axecosinussoft/CleanHeat/1. 3D Models/1.1 MVP-2 (Slider)/1.1.1 3D-Models — SolidWorks 2019/1. Детали/Модуль Micro зарядки Type С.SLDPRT

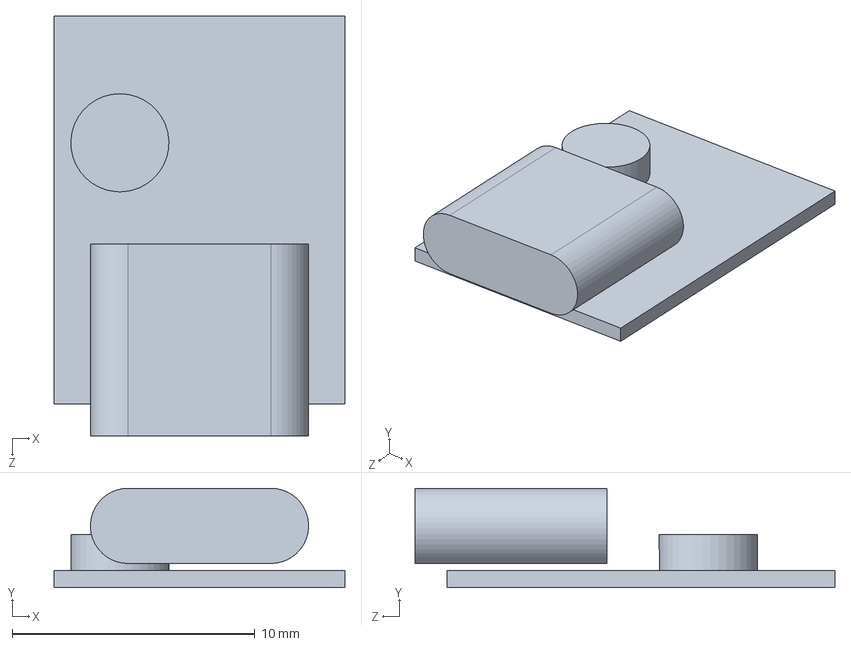
[picture p17: CAD file, 2026-01-13]
1. 3D Models/1.1 MVP-2 (Slider)/1.1.1 3D-Models — SolidWorks 2019/1. Детали/Модуль Micro зарядки Type С.SLDPRT
12.0 x 4.10 x 17.3 mm
