axecosinussoft/CleanHeat/1. 3D Models/1.1 MVP-2 (Slider)/1.1.2 3D-Print — STL/2. Каретка патрона form — Black.STL

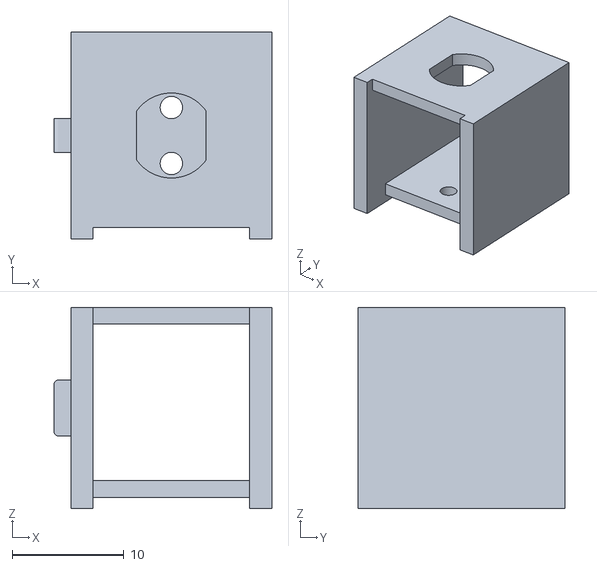
[picture p18: CAD file, 2026-01-13]
1. 3D Models/1.1 MVP-2 (Slider)/1.1.2 3D-Print — STL/2. Каретка патрона form — Black.STL
19.5 x 18.5 x 18.0
