axecosinussoft/CleanHeat/1. 3D Models/1.2 MVP-3 (Jazz)/1.2.2 3D-Print — STL/1. Корпус.STL

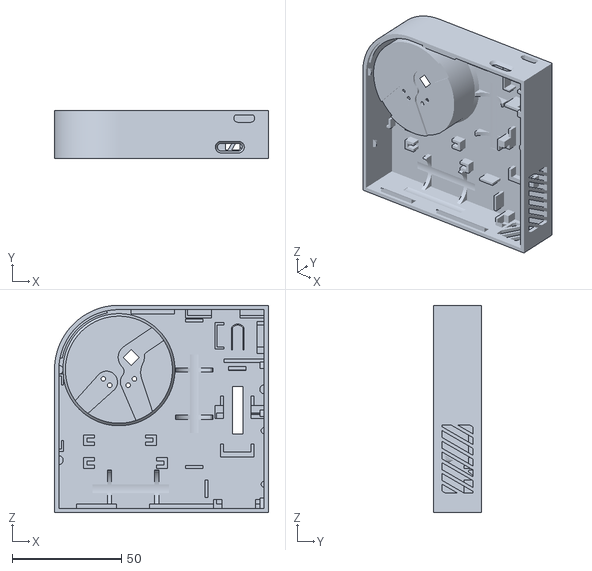
[picture p20: CAD file, 2026-01-13]
1. 3D Models/1.2 MVP-3 (Jazz)/1.2.2 3D-Print — STL/1. Корпус.STL
98.0 x 22.0 x 95.0
