axecosinussoft/CleanHeat/1. 3D Models/1.1 MVP-2 (Slider)/1.1.1 3D-Models — SolidWorks 2019/1. Детали/Патрон нити.SLDPRT

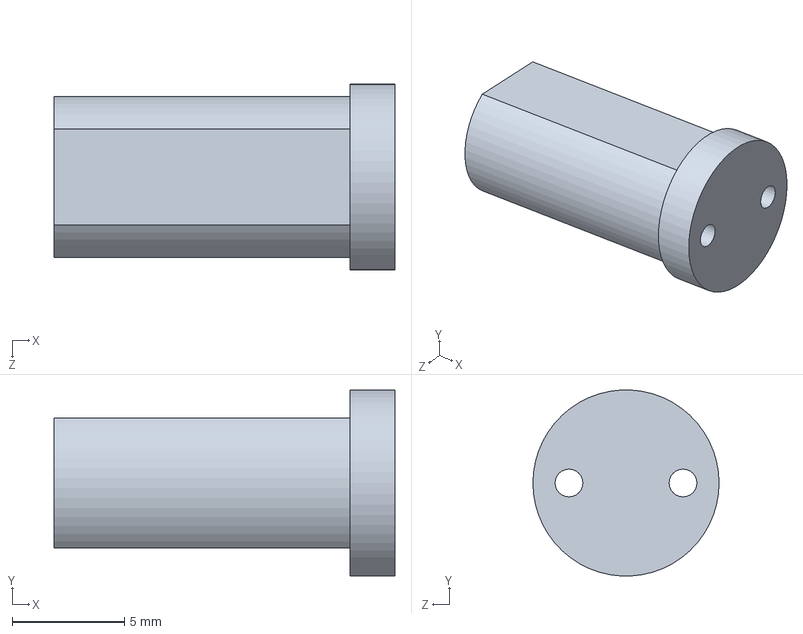
[picture p21: CAD file, 2026-01-13]
1. 3D Models/1.1 MVP-2 (Slider)/1.1.1 3D-Models — SolidWorks 2019/1. Детали/Патрон нити.SLDPRT
15.2 x 8.29 x 8.30 mm
