axecosinussoft/CleanHeat/1. 3D Models/1.2 MVP-3 (Jazz)/1.2.1 3D-Models — SolidWorks 2019/1. Детали/Wire1.SLDPRT

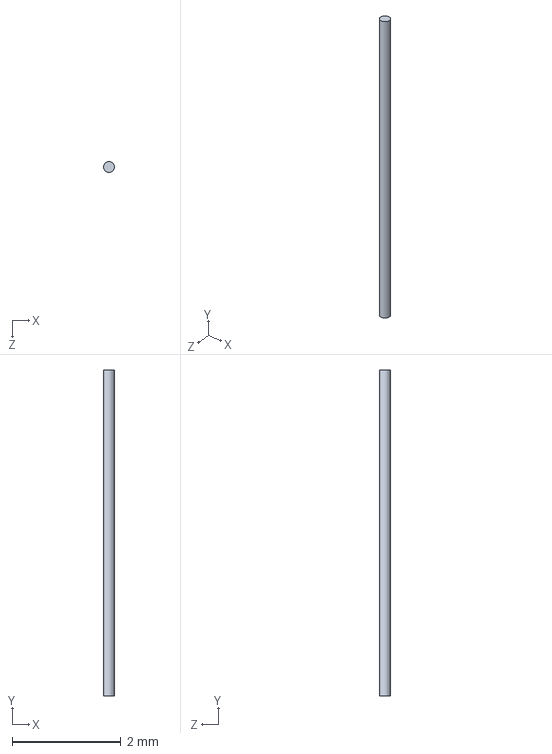
[picture p22: CAD file, 2026-01-13]
1. 3D Models/1.2 MVP-3 (Jazz)/1.2.1 3D-Models — SolidWorks 2019/1. Детали/Wire1.SLDPRT
0.2 x 6.00 x 0.2 mm
