axecosinussoft/CleanHeat/1. 3D Models/1.1 MVP-2 (Slider)/1.1.1 3D-Models — SolidWorks 2019/1. Детали/ESP32-C3-Zero.SLDPRT

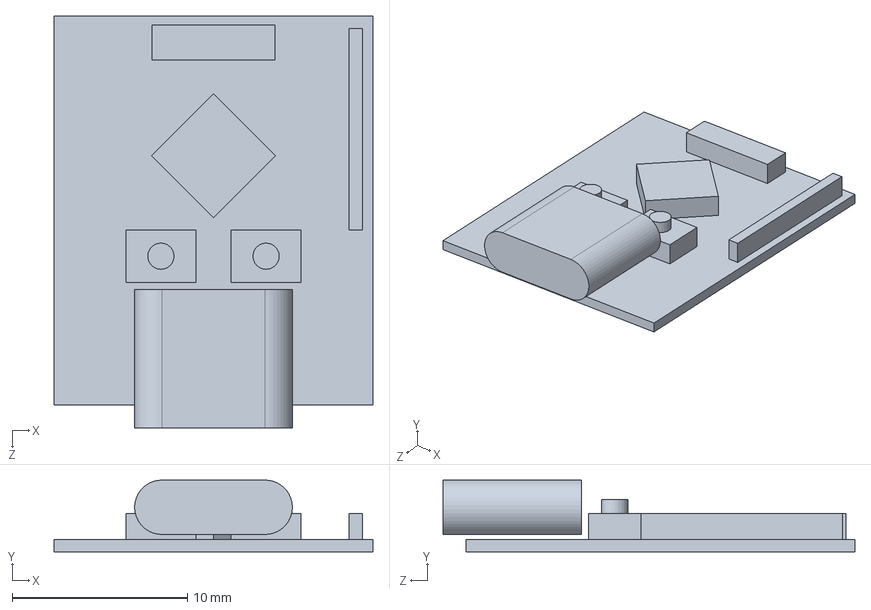
[picture p23: CAD file, 2026-01-13]
1. 3D Models/1.1 MVP-2 (Slider)/1.1.1 3D-Models — SolidWorks 2019/1. Детали/ESP32-C3-Zero.SLDPRT
18.2 x 4.10 x 23.5 mm
