axecosinussoft/CleanHeat/1. 3D Models/1.2 MVP-3 (Jazz)/1.2.1 3D-Models — SolidWorks 2019/1. Детали/Колпак.SLDPRT

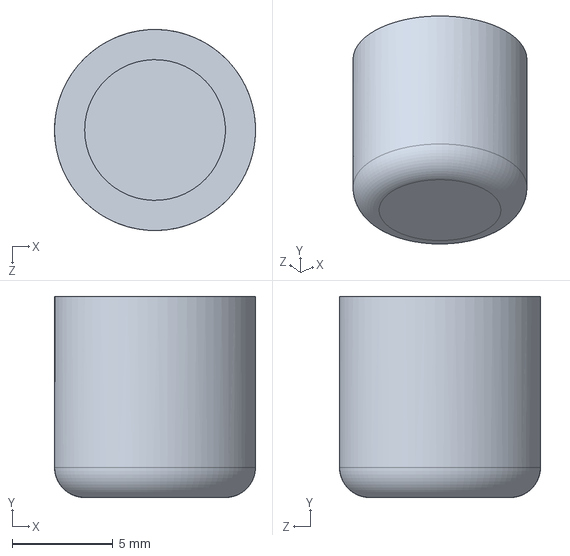
[picture p24: CAD file, 2026-01-13]
1. 3D Models/1.2 MVP-3 (Jazz)/1.2.1 3D-Models — SolidWorks 2019/1. Детали/Колпак.SLDPRT
10.00 x 10.0 x 10.00 mm
