axecosinussoft/CleanHeat/1. 3D Models/1.2 MVP-3 (Jazz)/1.2.2 3D-Print — STL/3. Подставка микрика.STL

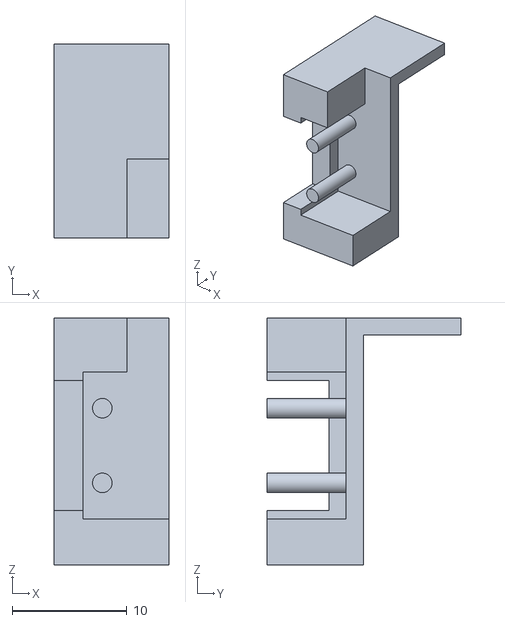
[picture p25: CAD file, 2026-01-13]
1. 3D Models/1.2 MVP-3 (Jazz)/1.2.2 3D-Print — STL/3. Подставка микрика.STL
10.0 x 16.9 x 21.5
