axecosinussoft/CleanHeat/1. 3D Models/1.2 MVP-3 (Jazz)/1.2.2 3D-Print — STL/4. Переключатель питания.STL

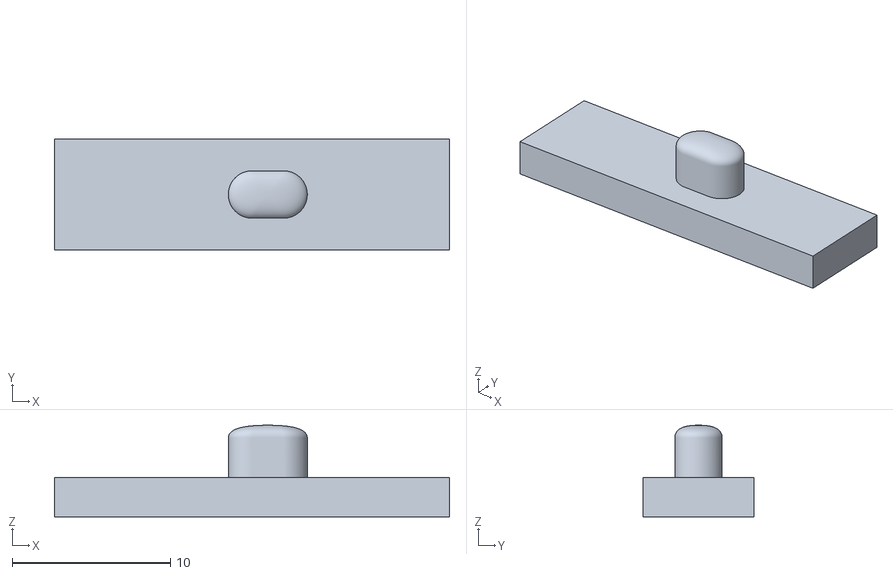
[picture p27: CAD file, 2026-01-13]
1. 3D Models/1.2 MVP-3 (Jazz)/1.2.2 3D-Print — STL/4. Переключатель питания.STL
25.0 x 7.00 x 5.80
