axecosinussoft/CleanHeat/1. 3D Models/1.1 MVP-2 (Slider)/1.1.1 3D-Models — SolidWorks 2019/1. Детали/Модуль зарядки Type С.SLDPRT

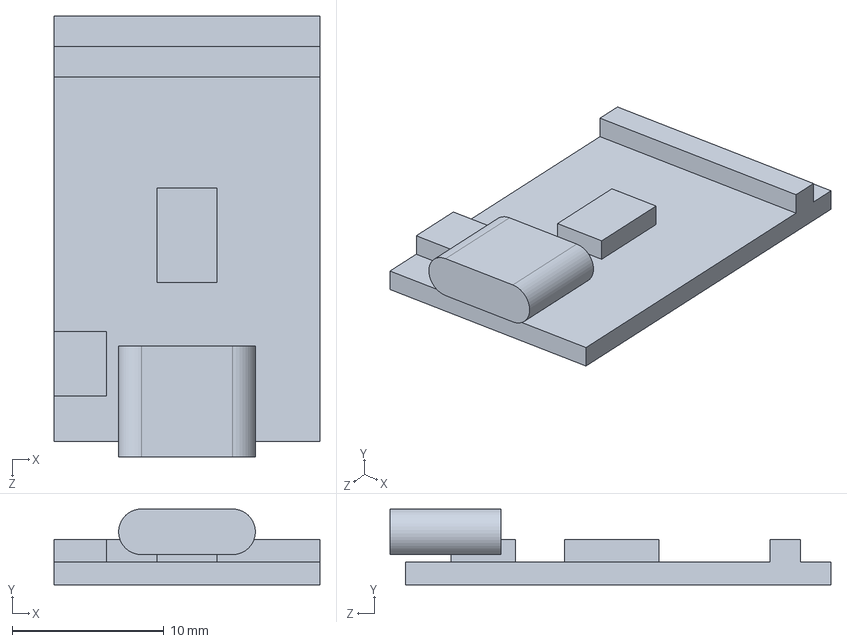
[picture p28: CAD file, 2026-01-13]
1. 3D Models/1.1 MVP-2 (Slider)/1.1.1 3D-Models — SolidWorks 2019/1. Детали/Модуль зарядки Type С.SLDPRT
17.5 x 5.00 x 29.0 mm
