axecosinussoft/CleanHeat/1. 3D Models/1.2 MVP-3 (Jazz)/1.2.1 3D-Models — SolidWorks 2019/1. Детали/4. Переключатель питания.SLDPRT

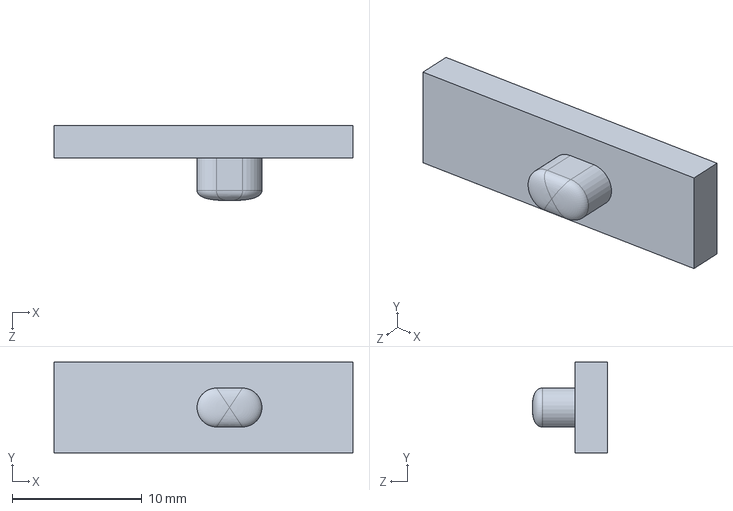
[picture p29: CAD file, 2026-01-13]
1. 3D Models/1.2 MVP-3 (Jazz)/1.2.1 3D-Models — SolidWorks 2019/1. Детали/4. Переключатель питания.SLDPRT
23.0 x 7.00 x 5.80 mm
