axecosinussoft/CleanHeat/1. 3D Models/1.1 MVP-2 (Slider)/1.1.1 3D-Models — SolidWorks 2019/1. Детали/Кнопка MSW-13.SLDPRT

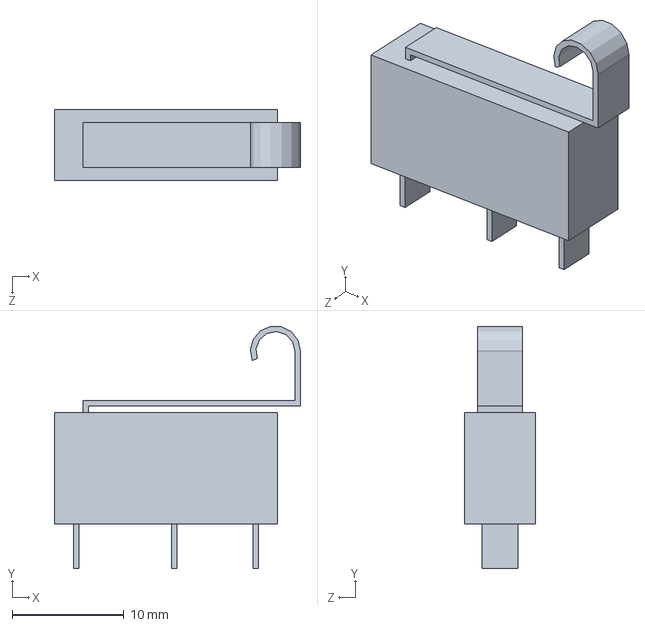
[picture p30: CAD file, 2026-01-13]
1. 3D Models/1.1 MVP-2 (Slider)/1.1.1 3D-Models — SolidWorks 2019/1. Детали/Кнопка MSW-13.SLDPRT
22.0 x 21.7 x 6.40 mm
