axecosinussoft/CleanHeat/1. 3D Models/1.2 MVP-3 (Jazz)/1.2.2 3D-Print — STL/7. Крышка нагревателя.STL

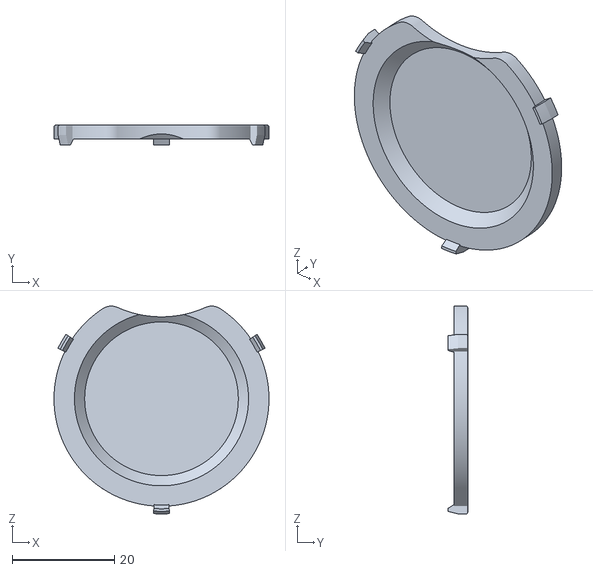
[picture p31: CAD file, 2026-01-13]
1. 3D Models/1.2 MVP-3 (Jazz)/1.2.2 3D-Print — STL/7. Крышка нагревателя.STL
42.0 x 4.00 x 40.6
