axecosinussoft/CleanHeat/1. 3D Models/1.2 MVP-3 (Jazz)/1.2.1 3D-Models — SolidWorks 2019/1. Детали/10.1 Шахта 1.SLDPRT

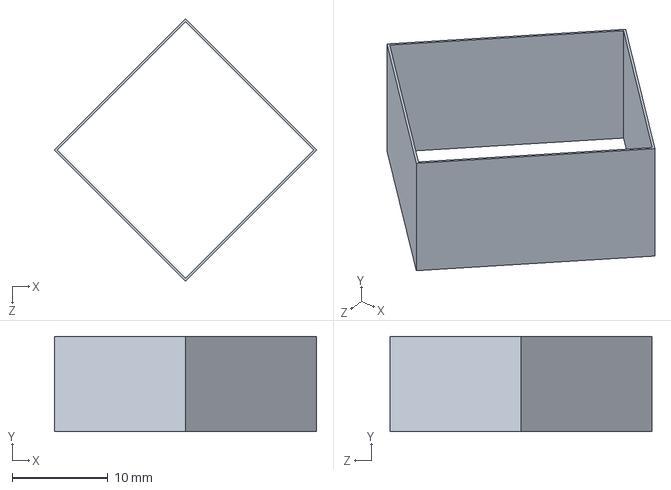
[picture p35: CAD file, 2026-01-13]
1. 3D Models/1.2 MVP-3 (Jazz)/1.2.1 3D-Models — SolidWorks 2019/1. Детали/10.1 Шахта 1.SLDPRT
27.4 x 10.0 x 27.4 mm
