axecosinussoft/CleanHeat/1. 3D Models/1.2 MVP-3 (Jazz)/1.2.2 3D-Print — STL/3.1 Подставка микрика fix.STL

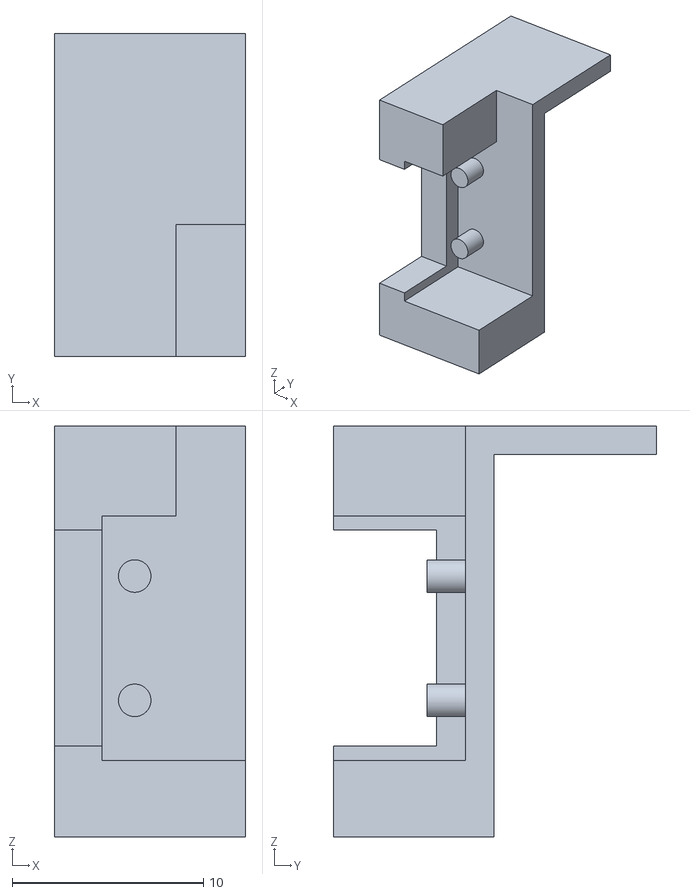
[picture p36: CAD file, 2026-01-13]
1. 3D Models/1.2 MVP-3 (Jazz)/1.2.2 3D-Print — STL/3.1 Подставка микрика fix.STL
10.0 x 16.9 x 21.5
