axecosinussoft/CleanHeat/1. 3D Models/1.2 MVP-3 (Jazz)/1.2.1 3D-Models — SolidWorks 2019/1. Детали/2.2 Пластина-фиксатор колпака.SLDPRT

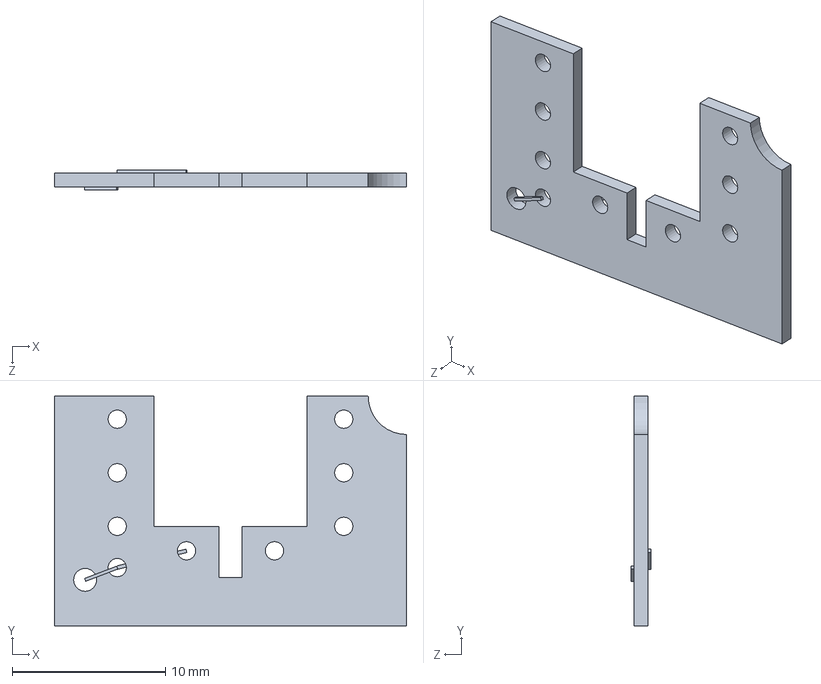
[picture p38: CAD file, 2026-01-13]
1. 3D Models/1.2 MVP-3 (Jazz)/1.2.1 3D-Models — SolidWorks 2019/1. Детали/2.2 Пластина-фиксатор колпака.SLDPRT
23.0 x 15.0 x 1.30 mm
