axecosinussoft/CleanHeat/1. 3D Models/1.1 MVP-2 (Slider)/1.1.1 3D-Models — SolidWorks 2019/1. Детали/Resistor 6.3 mm.SLDPRT

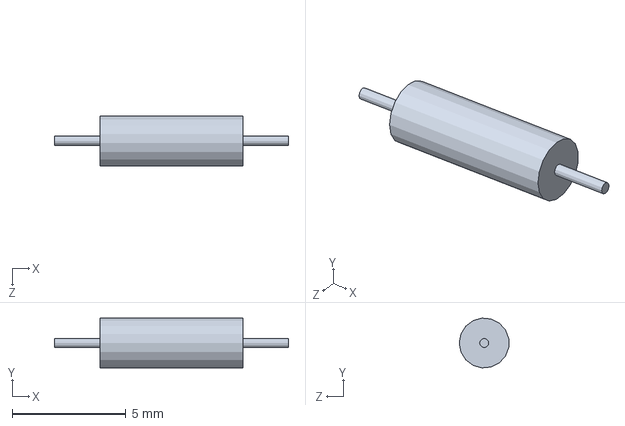
[picture p39: CAD file, 2026-01-13]
1. 3D Models/1.1 MVP-2 (Slider)/1.1.1 3D-Models — SolidWorks 2019/1. Детали/Resistor 6.3 mm.SLDPRT
10.3 x 2.19 x 2.18 mm
